mistic100/Nixie-Clock-IN12/Solidworks/air-case/leg-small.SLDPRT

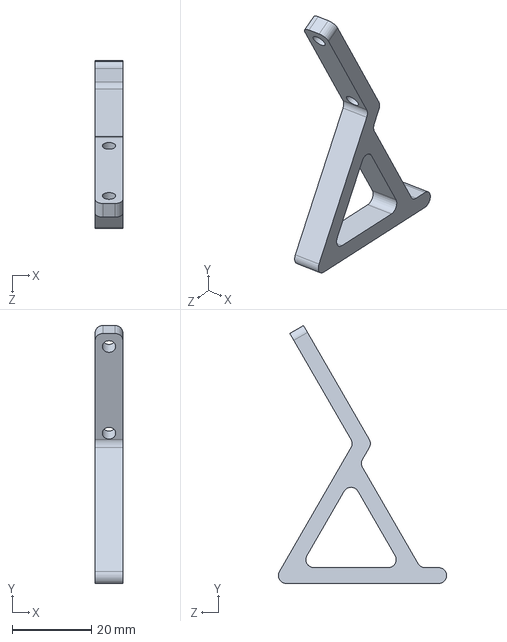
[picture p19: CAD file, 2021-09-05]
Solidworks/air-case/leg-small.SLDPRT
7.00 x 65.0 x 42.4 mm
