mistic100/Nixie-Clock-IN12/Solidworks/full-case/box.SLDPRT

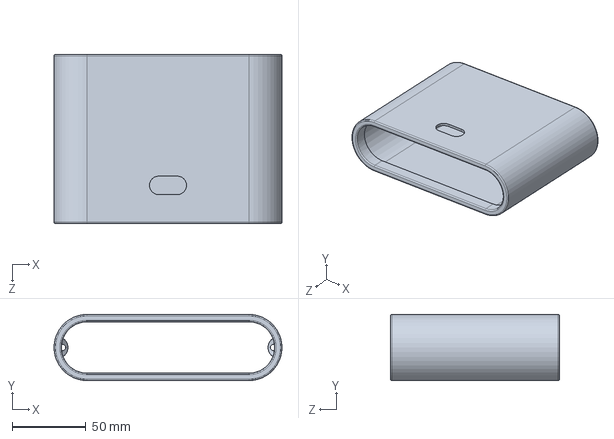
[picture p20: CAD file, 2021-10-05]
Solidworks/full-case/box.SLDPRT
155.0 x 45.0 x 115.0 mm
