mistic100/Nixie-Clock-IN12/Solidworks/full-case/front-panel.SLDPRT

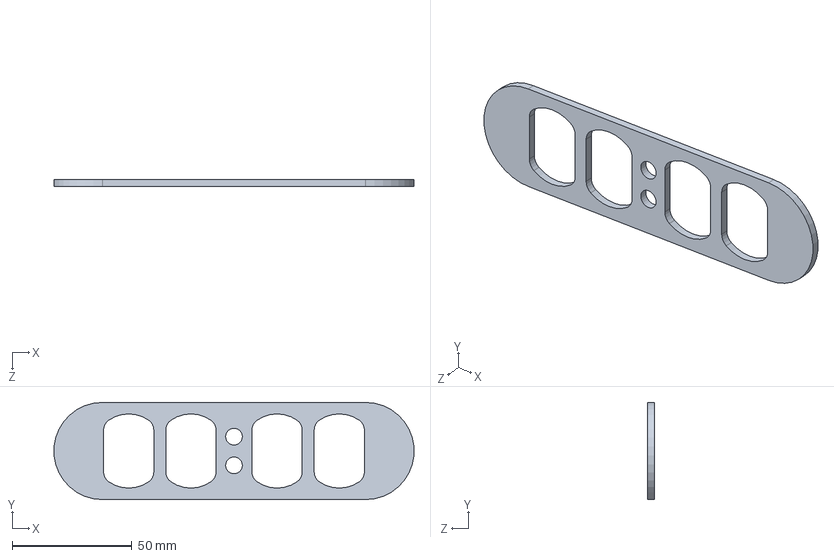
[picture p21: CAD file, 2021-10-05]
Solidworks/full-case/front-panel.SLDPRT
150.4 x 40.6 x 3.00 mm
